mjbots/quad/hw/chassis_a2/side_wall.3mf

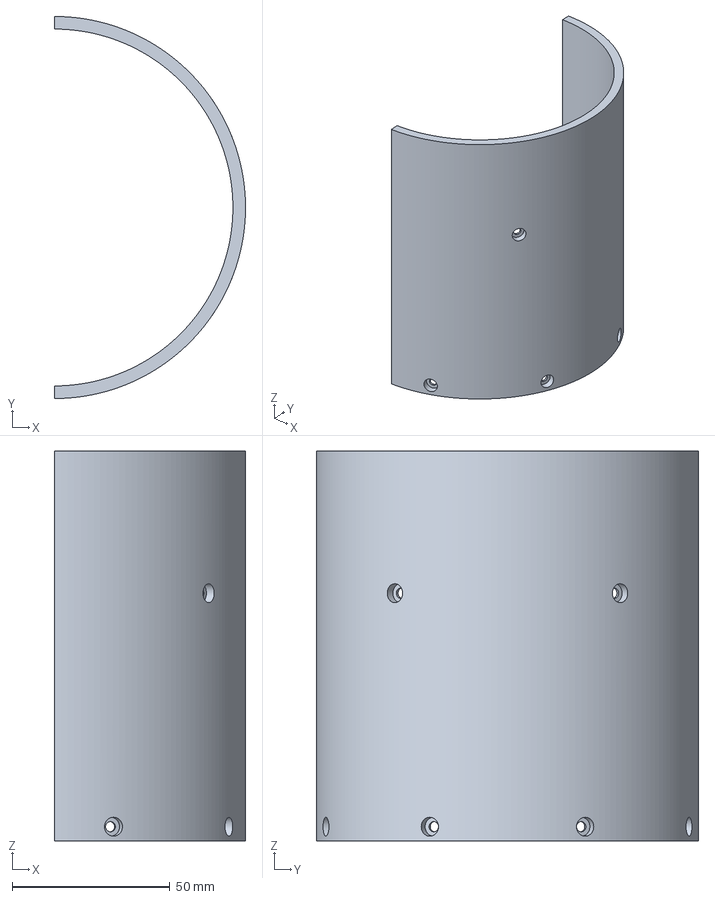
[picture p19: CAD file, 2022-05-17]
hw/chassis_a2/side_wall.3mf
60.5 x 121.0 x 123.5 mm
