mjbots/quad/hw/chassis_a2/bottom.3mf

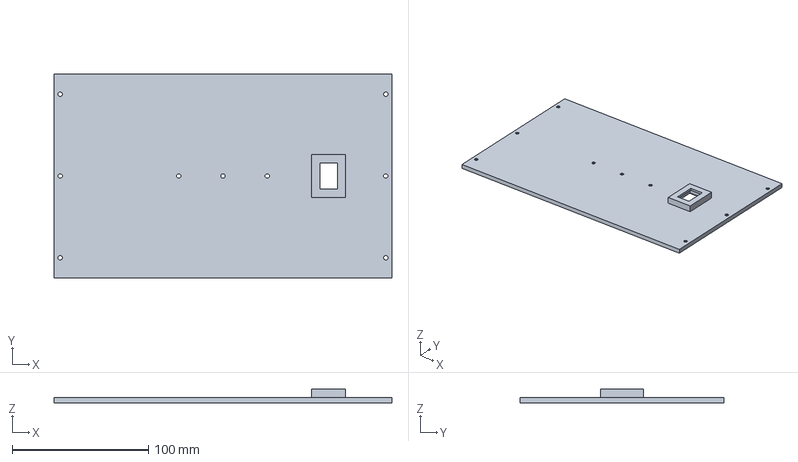
[picture p20: CAD file, 2022-05-17]
hw/chassis_a2/bottom.3mf
248.0 x 150.0 x 10.0 mm
