mjbots/quad/simulator/simulator_window.cc

// Copyright 2015-2020 Josh Pieper, jjp@pobox.com.
//
// Licensed under the Apache License, Version 2.0 (the "License");
// you may not use this file except in compliance with the License.
// You may obtain a copy of the License at
//
//     http://www.apache.org/licenses/LICENSE-2.0
//
// Unless required by applicable law or agreed to in writing, software
// distributed under the License is distributed on an "AS IS" BASIS,
// WITHOUT WARRANTIES OR CONDITIONS OF ANY KIND, either express or implied.
// See the License for the specific language governing permissions and
// limitations under the License.

#include "simulator_window.h"

#include <boost/filesystem.hpp>

#include <dart/dynamics/BoxShape.hpp>
#include <dart/dynamics/BodyNode.hpp>
#include <dart/dynamics/FreeJoint.hpp>
#include <dart/dynamics/RevoluteJoint.hpp>
#include <dart/dynamics/WeldJoint.hpp>
#include <dart/gui/LoadGlut.hpp>

#include "mjlib/base/fail.h"
#include "mjlib/base/json5_read_archive.h"
#include "mjlib/base/limit.h"
#include "mjlib/base/pid.h"
#include "mjlib/io/now.h"
#include "mjlib/io/debug_deadline_service.h"

#include "mjlib/micro/pool_ptr.h"
#include "mjlib/multiplex/micro_server.h"
#include "mjlib/multiplex/micro_datagram_server.h"

#include "base/common.h"
#include "base/context_full.h"

#include "mech/moteus.h"
#include "mech/quadruped.h"

#include "simulator/make_robot.h"

namespace dd = dart::dynamics;
namespace ds = dart::simulation;

using mjlib::base::Limit;

namespace mjmech {
namespace simulator {

namespace {

class Servo : public mjlib::multiplex::MicroServer::Server,
              public mjlib::multiplex::MicroDatagramServer {
 public:
  Servo(dd::Joint* joint, double sign,
        double max_torque_Nm)
      : joint_(joint),
        sign_(sign),
        max_torque_Nm_(max_torque_Nm) {
    server_.Start(this);
  }

  ~Servo() override {}

  void StartFrame() override {
  }

  Action CompleteFrame() override {
    return kAccept;
  }

  WriteAction Write(mjlib::multiplex::MicroServer::Register reg,
                    const mjlib::multiplex::MicroServer::Value& value) override {
    switch (static_cast<mech::moteus::Register>(reg)) {
      case mech::moteus::kMode: {
        const auto new_mode_int = mech::moteus::ReadInt(value);
        if (new_mode_int >= static_cast<int>(mech::moteus::Mode::kNumModes)) {
          return kNotWriteable;
        }
        staged_command_valid_ = true;
        staged_command_ = {};
        staged_command_.mode = static_cast<mech::moteus::Mode>(new_mode_int);
        return kSuccess;
      }
      case mech::moteus::kCommandPosition: {
        staged_command_.position = sign_ * mech::moteus::ReadPosition(value) / 360.0;
        return kSuccess;
      }
      case mech::moteus::kCommandVelocity: {
        staged_command_.velocity = sign_ * mech::moteus::ReadVelocity(value) / 360.0;
        return kSuccess;
      }
      case mech::moteus::kCommandPositionMaxTorque: {
        staged_command_.max_torque_Nm = mech::moteus::ReadTorque(value);
        return kSuccess;
      }
      case mech::moteus::kCommandStopPosition: {
        staged_command_.stop_position = sign_ * mech::moteus::ReadPosition(value) / 360.0;
        return kSuccess;
      }
      case mech::moteus::kCommandTimeout: {
        staged_command_.timeout_s = mech::moteus::ReadTime(value);
        return kSuccess;
      }
      case mech::moteus::kCommandFeedforwardTorque: {
        staged_command_.feedforward_Nm = sign_ * mech::moteus::ReadTorque(value);
        return kSuccess;
      }
      case mech::moteus::kCommandKpScale: {
        staged_command_.kp_scale = mech::moteus::ReadPwm(value);
        return kSuccess;
      }
      case mech::moteus::kCommandKdScale: {
        staged_command_.kd_scale = mech::moteus::ReadPwm(value);
        return kSuccess;
      }
      default: {
        break;
      }
    }
    return kSuccess;
  }

  mjlib::multiplex::MicroServer::ReadResult Read(
      mjlib::multiplex::MicroServer::Register reg,
      size_t type_int) const override {
    const auto type = static_cast<mech::moteus::RegisterTypes>(type_int);

    switch (static_cast<mech::moteus::Register>(reg)) {
      case mech::moteus::kMode: {
        return mech::moteus::WriteInt(static_cast<int8_t>(state_.mode), type);
      }
      case mech::moteus::kVoltage: {
        return mech::moteus::WriteVoltage(23.0, type);
      }
      case mech::moteus::kTemperature: {
        return mech::moteus::WriteTemperature(20.0, type);
      }
      case mech::moteus::kRezeroState: {
        return mech::moteus::WriteInt(2, type);
      }
      case mech::moteus::kFault: {
        return mech::moteus::WriteInt(0, type);
      }
      case mech::moteus::kRegisterMapVersion: {
        return mech::moteus::WriteInt(
            static_cast<int8_t>(mech::moteus::kCurrentRegisterMapVersion),
            type);
      }
      case mech::moteus::kPosition: {
        return mech::moteus::WritePosition(sign_ * 360.0 * position(), type);
      }
      case mech::moteus::kVelocity: {
        return mech::moteus::WriteVelocity(sign_ * 360.0 * velocity(), type);
      }
      case mech::moteus::kTorque: {
        return mech::moteus::WriteTorque(sign_ * current_torque_Nm_, type);
      }
      // case kQCurrent: {
      // }
      // case kDCurrent: {
      // }
      default: {
        return mech::moteus::WritePwm(0, type);
      }
    }
    return {};
  }

  void AsyncRead(Header* header,
                 const mjlib::base::string_span& read_buffer,
                 const mjlib::micro::SizeCallback& read_callback) override {
    BOOST_ASSERT(!read_header_);

    read_header_ = header;
    read_buffer_ = read_buffer;
    read_callback_ = read_callback;
  }

  void AsyncWrite(const Header& header,
                  const std::string_view& write_buffer,
                  const Header&,
                  const mjlib::micro::SizeCallback& write_callback) override {
    BOOST_ASSERT(!write_header_);

    write_header_ = header;
    write_buffer_ = write_buffer;
    write_callback_ = write_callback;
  }

  mjlib::multiplex::MicroDatagramServer::Properties
  properties() const override {
    return {};
  }

  void Request(const mjlib::multiplex::RegisterRequest& request,
               int id,
               mjlib::multiplex::AsioClient::Reply* reply,
               mjlib::base::error_code*) {
    BOOST_ASSERT(!!read_header_);

    // For simulation purposes, each servo thinks it is ID 1.
    read_header_->source = request.request_reply() ? 0x80 : 0x00;
    read_header_->destination = 1;
    read_header_->size = request.buffer().size();

    const auto to_read =
        std::min<size_t>(read_buffer_.size(), request.buffer().size());
    std::memcpy(read_buffer_.data(), request.buffer().data(), to_read);

    {
      auto read_copy = std::move(read_callback_);

      read_header_ = {};
      read_buffer_ = {};
      read_callback_ = {};

      read_copy(mjlib::micro::error_code(), to_read);
    }

    // This may have resulted in a write.

    if (write_header_) {

      mjlib::base::BufferReadStream stream{write_buffer_};
      parsed_data_.clear();
      mjlib::multiplex::ParseRegisterReply(stream, &parsed_data_);
      for (const auto& item : parsed_data_) {
        reply->push_back({static_cast<uint8_t>(id), item.first, item.second});
      }

      {
        auto write_copy = std::move(write_callback_);

        write_header_ = {};
        write_buffer_ = {};
        write_callback_ = {};

        write_copy(mjlib::micro::error_code(), stream.offset());
      }
    }

    Update();
  }

  void Run(double dt_s) {
    // In case nothing else sets it.
    current_torque_Nm_ = 0.0;

    switch (state_.mode) {
      case mech::moteus::Mode::kStopped: {
        joint_->setForce(0, 0.0);
        state_.control_position = std::numeric_limits<double>::quiet_NaN();
        break;
      }
      case mech::moteus::Mode::kPosition: {
        RunPosition(dt_s);
        break;
      }
      case mech::moteus::Mode::kZeroVelocity: {
        RunZeroVelocity(dt_s);
        state_.control_position = std::numeric_limits<double>::quiet_NaN();
        break;
      }
      default: {
        state_.control_position = std::numeric_limits<double>::quiet_NaN();
        break;
      }
    }
  }

 private:
  double position() const {
    return joint_->getPosition(0) / (2.0 * M_PI);
  }

  double velocity() const {
    return joint_->getVelocity(0) / (2.0 * M_PI);
  }

  void RunZeroVelocity(double dt_s) {
    mjlib::base::PID::ApplyOptions apply_options;
    apply_options.kp_scale = 0.0;
    apply_options.kd_scale = command_.kd_scale;

    RunPositionCommon(dt_s, apply_options);
  }

  void RunPosition(double dt_s) {
    mjlib::base::PID::ApplyOptions apply_options;
    apply_options.kp_scale = command_.kp_scale;
    apply_options.kd_scale = command_.kd_scale;

    RunPositionCommon(dt_s, apply_options);
  }

  void RunPositionCommon(
      double dt_s,
      const mjlib::base::PID::ApplyOptions& apply_options) {
    if (!std::isnan(command_.position)) {
      state_.control_position = command_.position;
      command_.position = std::numeric_limits<float>::quiet_NaN();
    } else if (std::isnan(state_.control_position)) {
      state_.control_position = position();
    }

    auto velocity_command = command_.velocity;

    const auto old_position = state_.control_position;
    state_.control_position =
        Limit(state_.control_position + velocity_command * dt_s,
              position_min_, position_max_);
    if (!std::isnan(command_.stop_position)) {
      if ((state_.control_position -
           command_.stop_position) * velocity_command > 0.0) {
        // We are moving away from the stop position.  Force it to be there.
        state_.control_position = command_.stop_position;
      }
    }
    if (state_.control_position == old_position) {
      // We have hit a limit.
      velocity_command = 0.0;
    }

    const double unlimited_torque_Nm =
        pid_position_.Apply(position(), state_.control_position,
                            velocity(), velocity_command,
                            1.0 / dt_s,
                            apply_options) +
        command_.feedforward_Nm;

    const double limited_torque_Nm =
        Limit(unlimited_torque_Nm, -command_.max_torque_Nm,
              command_.max_torque_Nm);

    const double physical_torque_Nm =
        Limit(limited_torque_Nm, -max_torque_Nm_, max_torque_Nm_);

    current_torque_Nm_ = physical_torque_Nm;
    joint_->setForce(0, physical_torque_Nm);
  }

  void Update() {
    if (staged_command_valid_) {
      // Update with the new command.
      staged_command_valid_ = false;
      command_ = staged_command_;

      // The simulation doesn't have a state machine yet.  We just
      // instantly switch to whatever we are commanded.
      state_.mode = command_.mode;

      if (std::isnan(command_.position) &&
          !std::isnan(command_.stop_position) &&
          !std::isnan(command_.velocity) &&
          command_.velocity != 0.0) {
        command_.velocity = std::abs(command_.velocity) *
            ((command_.stop_position > position()) ? 1.0 : -1.0);
      }
    }

    staged_command_ = {};
  }

  dd::Joint* const joint_;
  const double sign_;
  const double max_torque_Nm_;
  mjlib::micro::SizedPool<16384> pool_;
  mjlib::multiplex::MicroServer server_{&pool_, this, {}};

  Header* read_header_ = nullptr;
  mjlib::base::string_span read_buffer_;
  mjlib::micro::SizeCallback read_callback_;

  std::optional<Header> write_header_;
  std::string_view write_buffer_;
  mjlib::micro::SizeCallback write_callback_;

  struct State {
    mech::moteus::Mode mode = mech::moteus::Mode::kStopped;
    double control_position = std::numeric_limits<double>::quiet_NaN();

    mjlib::base::PID::State pid_position;
  };

  State state_;

  mjlib::base::PID::Config pid_position_config_ = []() {
      mjlib::base::PID::Config config;
      config.kp = 50.0;
      config.ki = 100.0;
      config.ilimit = 0.0;
      config.kd = 9.0f;
      config.sign = -1.0;
      return config;
  }();

  mjlib::base::PID pid_position_{
    &pid_position_config_, &state_.pid_position};

  struct Command {
    mech::moteus::Mode mode = mech::moteus::Mode::kStopped;

    double position = 0.0f;
    double velocity = 0.0f;

    double max_torque_Nm = 100.0f;
    double stop_position = std::numeric_limits<double>::quiet_NaN();
    double feedforward_Nm = 0.0f;

    double kp_scale = 1.0f;
    double kd_scale = 1.0f;

    double timeout_s = 0.0f;
  };

  Command staged_command_;
  bool staged_command_valid_ = false;

  Command command_;

  double current_torque_Nm_ = 0.0;

  const double position_min_ = -1.0;
  const double position_max_ = 1.0;

  std::vector<mjlib::multiplex::RegisterValue> parsed_data_;
};

class SimPi3hat : public mech::Pi3hatInterface {
 public:
  struct Options {
    double torque_scale = 1.0;
    double yaw_offset_rad = 0.0;

    template <typename Archive>
    void Serialize(Archive* a) {
      a->Visit(MJ_NVP(torque_scale));
      a->Visit(MJ_NVP(yaw_offset_rad));
    }
  };

  SimPi3hat(boost::asio::any_io_executor executor, const Options& options)
      : executor_(executor),
        options_(options) {}
  ~SimPi3hat() override {}

  void set_frame(dd::Frame* frame) {
    frame_ = frame;
  }

  void DoAttitude(mech::AttitudeData* attitude) {
    if (frame_) {
      attitude->timestamp = mjlib::io::Now(executor_.context());

      // DART uses a coordinate system where +Z is up.  The robot
      // expects its coordinate system to be with +Z down.  The legs
      // are already modeled inverted.  Thus we have a confusing set
      // of transforms to get everything into an appropriate frame.

      const Eigen::AngleAxisd mount(0, Eigen::Vector3d::UnitX());

      const Eigen::Isometry3d tf = frame_->getTransform() * mount;
      base::Quaternion mirror_quaternion =
          Sophus::SE3d(tf.matrix()).unit_quaternion();
      // https://stackoverflow.com/questions/32438252/efficient-way-to-apply-mirror-effect-on-quaternion-rotation
      attitude->attitude =
          base::Quaternion::FromAxisAngle(options_.yaw_offset_rad, 0, 0, 1) *
          base::Quaternion(
              mirror_quaternion.w(),
              -mirror_quaternion.x(),
              -mirror_quaternion.y(),
              mirror_quaternion.z());
      attitude->euler_deg = (180.0 / M_PI) * attitude->attitude.euler_rad();

      const Eigen::Vector3d rate_rps =
          mount * frame_->getAngularVelocity();
      attitude->rate_dps.x() = -base::Degrees(rate_rps[0]);
      attitude->rate_dps.y() = -base::Degrees(rate_rps[1]);
      attitude->rate_dps.z() = base::Degrees(rate_rps[2]);

      Eigen::Vector3d accel =
          mount * frame_->getLinearAcceleration(Eigen::Vector3d(0, 0, 0));
      attitude->accel_mps2 = -1.0 * accel;
    } else {
      *attitude = {};
    }

  }

  void ReadImu(mech::AttitudeData* attitude,
               mjlib::io::ErrorCallback callback) override {
    DoAttitude(attitude);
    boost::asio::post(
        executor_,
        std::bind(std::move(callback), mjlib::base::error_code()));
  }

  // ***********************
  // RfClient

  void AsyncWaitForSlot(int*, uint16_t* bitfield, mjlib::io::ErrorCallback) override {
  }

  Slot rx_slot(int, int slot_idx) override {
    return slot_;
  }

  void tx_slot(int, int slot_id, const Slot&) override {
  }

  Slot tx_slot(int, int slot_idx) override {
    return slot_;
  }


  // Selector

  void AsyncStart(mjlib::io::ErrorCallback callback) {
    boost::asio::post(
        executor_,
        std::bind(std::move(callback), mjlib::base::error_code()));
  }

  void set_data(const mech::AttitudeData& data) {
    data_ = data;
  }

  // ***********************
  // multiplex::AsioClient

  void DoCan(const Request* request, Reply* reply,
             mjlib::base::error_code* ec) {
    *reply = {};
    for (const auto& id_request : *request) {
      DoRequest(id_request, reply, ec);
    }
  }

  void AsyncTransmit(
      const Request* request, Reply* reply,
      mjlib::io::ErrorCallback callback) override {
    mjlib::base::error_code ec;
    DoCan(request, reply, &ec);
    boost::asio::post(
        executor_,
        std::bind(std::move(callback), ec));
  }

  mjlib::io::SharedStream MakeTunnel(
      uint8_t id, uint32_t channel, const TunnelOptions& options) override {
    return {};
  }

  void AddServo(dd::Joint* joint, int id,
                double lower_limit, double upper_limit) {
    const double sign = signs_.at(id);
    servos_[id] = std::make_unique<Servo>(
        joint, sign, options_.torque_scale * torque_Nm_.at(id));
    joint->setLimitEnforcement(true);
    if (std::isfinite(lower_limit)) {
      if (sign > 0.0) {
        joint->setPositionLowerLimit(0, lower_limit);
        joint->setPositionUpperLimit(0, upper_limit);
      } else {
        joint->setPositionLowerLimit(0, -upper_limit);
        joint->setPositionUpperLimit(0, -lower_limit);
      }
    }
    joint->setVelocityLowerLimit(0, -base::Radians(speed_dps_.at(id)));
    joint->setVelocityUpperLimit(0, base::Radians(speed_dps_.at(id)));
  }

  void Run(double dt_s) {
    for (auto& pair : servos_) {
      pair.second->Run(dt_s);
    }
  }

  void Cycle(mech::AttitudeData* attitude,
             const Request* request, Reply* reply,
             mjlib::io::ErrorCallback callback) override {
    DoAttitude(attitude);
    mjlib::base::error_code ec;
    DoCan(request, reply, &ec);

    boost::asio::post(
        executor_,
        std::bind(std::move(callback), ec));
  }

 private:
  void DoRequest(const mjlib::multiplex::AsioClient::IdRequest& id_request,
                 mjlib::multiplex::AsioClient::Reply* reply,
                 mjlib::base::error_code* ec) {
    const auto id = id_request.id;
    const auto it = servos_.find(id);
    if (it == servos_.end()) {
      // We don't have this servo.
      *ec = mjlib::base::error_code::einval(
          fmt::format("unknown servo {}", id));
      return;
    }

    it->second->Request(id_request.request, id, reply, ec);
  }

  boost::asio::any_io_executor executor_;
  const Options options_;
  std::map<int, std::unique_ptr<Servo>> servos_;

  std::map<int, double> signs_{
    {1, 1.0},
    {2, 1.0},
    {3, 1.0},
    {4, -1.0},
    {5, -1.0},
    {6, 1.0},
    {7, -1.0},
    {8, -1.0},
    {9, 1.0},
    {10, 1.0},
    {11, 1.0},
    {12, 1.0},
        };

  std::map<int, double> torque_Nm_{
    {1, 12.5},
    {2, 22.2},
    {3, 12.5},
    {4, 12.5},
    {5, 22.2},
    {6, 12.5},
    {7, 12.5},
    {8, 22.2},
    {9, 12.5},
    {10, 12.5},
    {11, 22.2},
    {12, 12.5},
        };

  std::map<int, double> speed_dps_{
    {1, 2400},
    {2, 1350},
    {3, 2400},
    {4, 2400},
    {5, 1350},
    {6, 2400},
    {7, 2400},
    {8, 1350},
    {9, 2400},
    {10, 2400},
    {11, 1350},
    {12, 2400},
  };

  mech::AttitudeData data_;
  dd::Frame* frame_ = nullptr;
  Slot slot_;
};
}

struct Options {
  bool start_disabled = false;
  std::string config = "configs/quada1.cfg";
  double torque_scale = 1.0;
  double ramp_height = 0.1;
  int ramp = 1;

  template <typename Archive>
  void Serialize(Archive* a) {
    a->Visit(MJ_NVP(start_disabled));
    a->Visit(MJ_NVP(config));
    a->Visit(MJ_NVP(torque_scale));
    a->Visit(MJ_NVP(ramp_height));
    a->Visit(MJ_NVP(ramp));
  }
};

class SimulatorWindow::Impl : public dart::gui::glut::SimWindow {
 public:
  static Impl* g_impl_;

  Impl(base::Context& context)
      : context_(context.context),
        executor_(context.executor),
        quadruped_(context) {
    g_impl_ = this;
    mDisplayTimeout = 10;
    world_->setTimeStep(0.0001);

    quadruped_.m()->pi3hat->Register<SimPi3hat>("sim");
    quadruped_.m()->pi3hat->set_default("sim");

    floor_ = MakeFloor();
    {
      std::ifstream inf(options_.config);
      mjlib::base::system_error::throw_if(
          !inf.is_open(),
          fmt::format("could not open config file '{}'", options_.config));
      mjlib::base::Json5ReadArchive(inf).Accept(&quadruped_config_);
    }

    robot_ = MakeRobot(quadruped_config_);

    world_->addSkeleton(floor_);
    world_->addSkeleton(robot_);

    setWorld(world_);
  }

  void AsyncStart(mjlib::io::ErrorCallback callback) {
    if (options_.ramp) {
      ramp_ = MakeRamp(options_.ramp_height);
      world_->addSkeleton(ramp_);
    }

    // The GLUT timer will actually process our event loop, so it
    // needs to be going right away.
    StartGlutTimer();

    if (!options_.start_disabled) {
      // Send a space bar to get us simulating.
      SimWindow::keyboard(' ', 0, 0);
    }

    quadruped_.AsyncStart([this, callback=std::move(callback)](
                              const auto& ec) mutable {
        this->HandleStart(ec, std::move(callback));
      });
  }

  void HandleStart(const mjlib::base::error_code& ec,
                   mjlib::io::ErrorCallback callback) {
    if (ec) {
      boost::asio::post(
          executor_,
          std::bind(std::move(callback), ec));
      return;
    }

    pi3hat_ = dynamic_cast<SimPi3hat*>(quadruped_.m()->pi3hat->selected());
    BOOST_ASSERT(pi3hat_);

    pi3hat_->set_frame(robot_->getBodyNode("robot"));

    for (int leg = 0; leg < 4; leg++) {
      const auto& leg_config = quadruped_config_.legs.at(leg);

      std::string leg_prefix = fmt::format("leg{}", leg);
      auto add_servo = [&](auto name, auto id, double lower, double upper) {
        auto* const joint = robot_->getBodyNode(leg_prefix + name)->getParentJoint();
        pi3hat_->AddServo(joint, id, lower, upper);
      };
      constexpr auto kNaN = std::numeric_limits<double>::signaling_NaN();
      add_servo("_shoulder", leg_config.ik.shoulder.id, kNaN, kNaN);
      add_servo("_femur", leg_config.ik.femur.id, kNaN, kNaN);
      add_servo("_tibia", leg_config.ik.tibia.id,
                base::Radians(-140), base::Radians(140));
    }

    boost::asio::post(
        executor_,
        std::bind(std::move(callback), ec));
  }

  static void GlobalHandleGlutTimer(int) {
    g_impl_->HandleGlutTimer();
  }

  void StartGlutTimer() {
    glutTimerFunc(1, &GlobalHandleGlutTimer, 0);
  }

  void HandleGlutTimer() {
    context_.poll();
    context_.reset();
    StartGlutTimer();
  }

  void timeStepping() override {
    const double dt_s = world_->getTimeStep();

    debug_time_->SetTime(debug_time_->now() +
                         mjlib::base::ConvertSecondsToDuration(dt_s));
    context_.poll();
    context_.reset();

    pi3hat_->Run(dt_s);

    SimWindow::timeStepping();

    mTrans = -1000.0 * robot_->getBodyNode("robot")->getTransform().translation();
  }

  boost::asio::io_context& context_;
  boost::asio::any_io_executor executor_;
  mjlib::io::DebugDeadlineService* const debug_time_ =
      mjlib::io::DebugDeadlineService::Install(context_);
  const bool set_time_ = [this]() {
    debug_time_->SetTime(
        boost::posix_time::microsec_clock::universal_time() +
        boost::posix_time::hours(
            static_cast<int>(24 * 365.25 * 10)));
    return true;
  }();

  Options options_;

  dd::SkeletonPtr floor_;
  dd::SkeletonPtr robot_;
  dd::SkeletonPtr ramp_;

  ds::WorldPtr world_ = std::make_shared<ds::World>();

  mech::QuadrupedConfig quadruped_config_;
  mech::Quadruped quadruped_;

  SimPi3hat* pi3hat_ = nullptr;
};

SimulatorWindow::Impl* SimulatorWindow::Impl::g_impl_ = nullptr;

SimulatorWindow::SimulatorWindow(base::Context& context)
    : impl_(std::make_unique<Impl>(context)) {}

SimulatorWindow::~SimulatorWindow() {}

clipp::group SimulatorWindow::program_options() {
  return clipp::group(
      mjlib::base::ClippArchive().Accept(&impl_->options_).release(),
      impl_->quadruped_.program_options());
}

void SimulatorWindow::AsyncStart(mjlib::io::ErrorCallback callback) {
  impl_->AsyncStart(std::move(callback));
}

void SimulatorWindow::InitWindow(int x, int y, const char* name) {
  impl_->initWindow(x, y, name);
}

}
}
